ifilot/gameboy-cartridge-reader/gui/img/flash_cartridge_at28c256.png

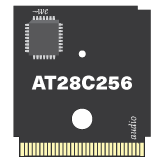
gui/img/flash_cartridge_at28c256.png
