ifilot/gameboy-cartridge-reader/gui/img/sst39sf010_flash_cartridge.png

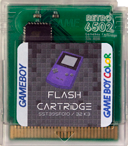
gui/img/sst39sf010_flash_cartridge.png
